hpoleselo/SSFR/latex/imagens/kpeKi.jpg

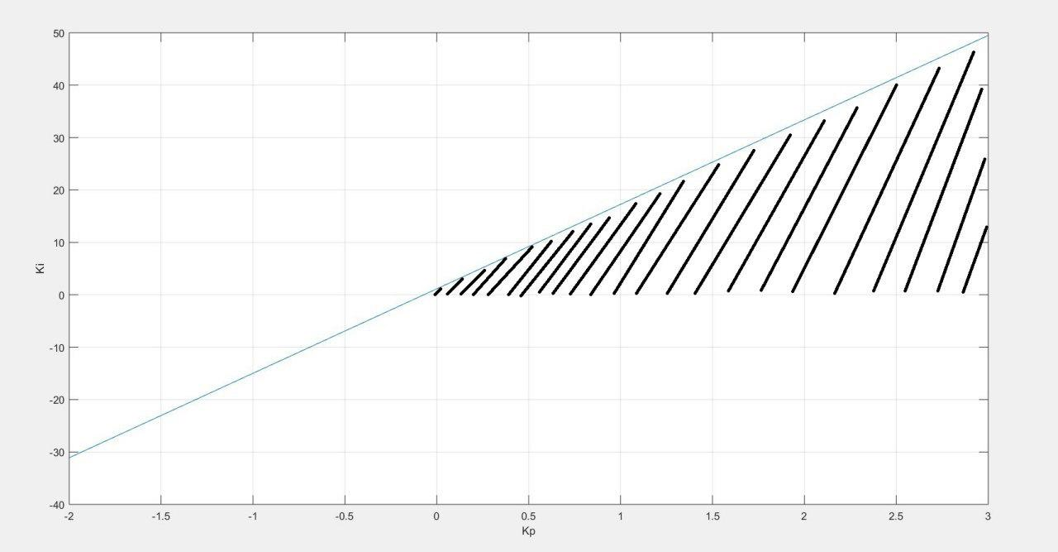
latex/imagens/kpeKi.jpg
