hpoleselo/SSFR/src/calib_images/left-0000.png

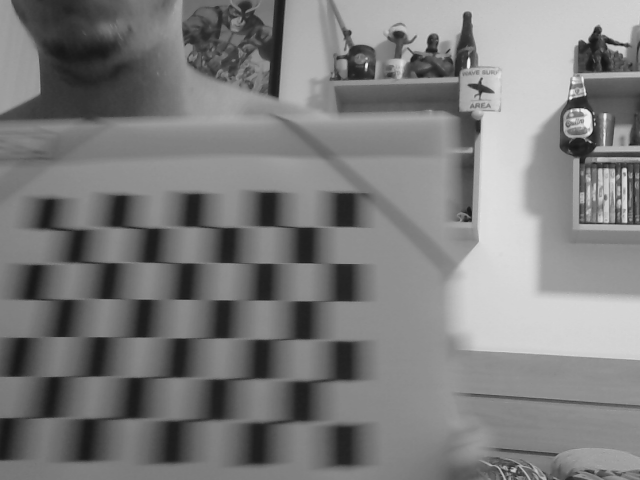
src/calib_images/left-0000.png
