hpoleselo/SSFR/src/calib_images/left-0001.png

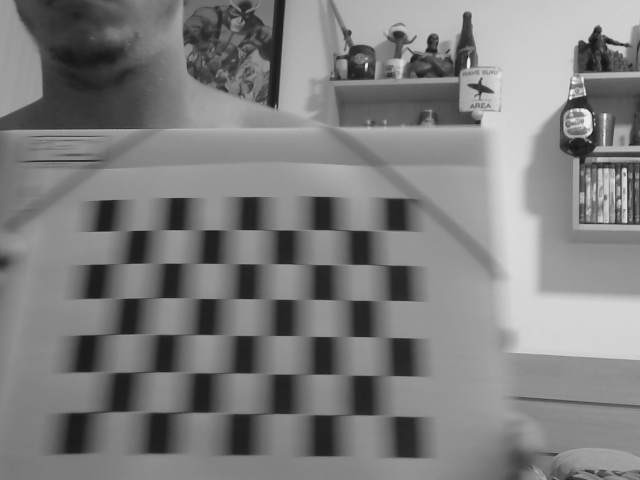
src/calib_images/left-0001.png
