hpoleselo/SSFR/src/calib_images/left-0002.png

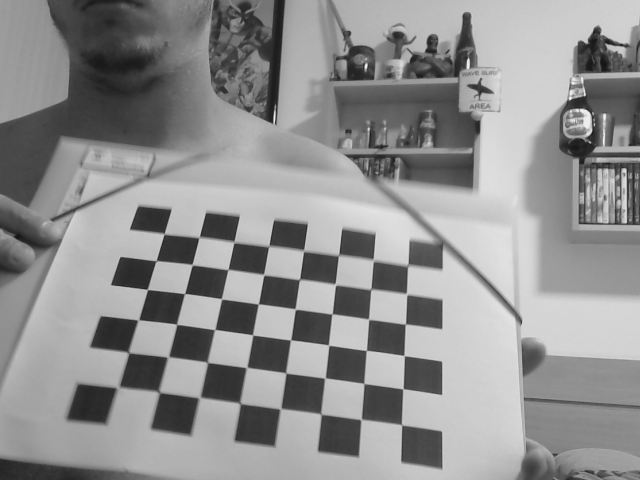
src/calib_images/left-0002.png
