hpoleselo/SSFR/src/calib_images/left-0003.png

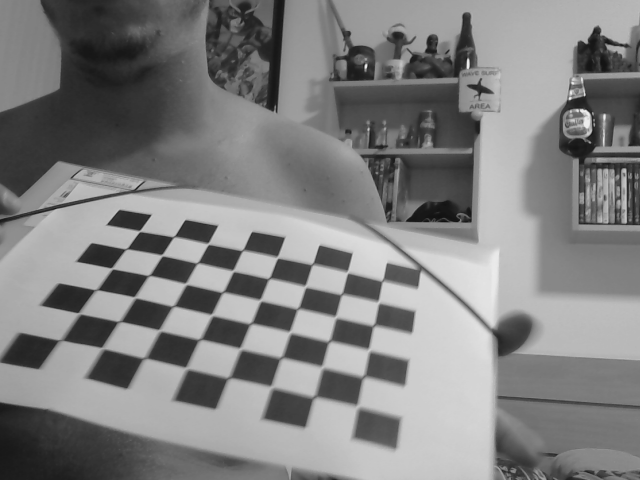
src/calib_images/left-0003.png
