hpoleselo/SSFR/src/calib_images/left-0004.png

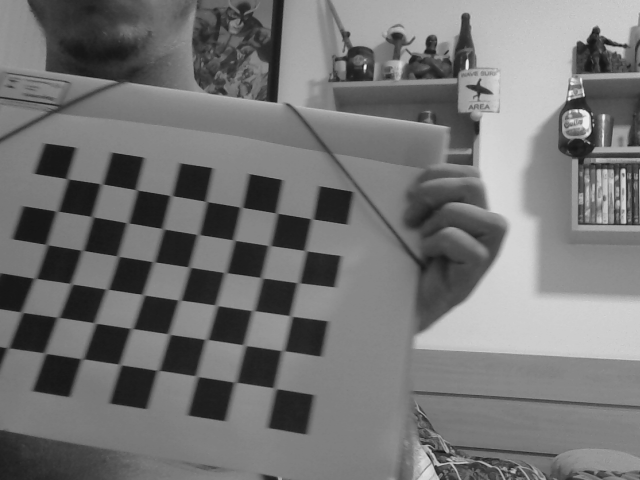
src/calib_images/left-0004.png
