hpoleselo/SSFR/src/calib_images/left-0005.png

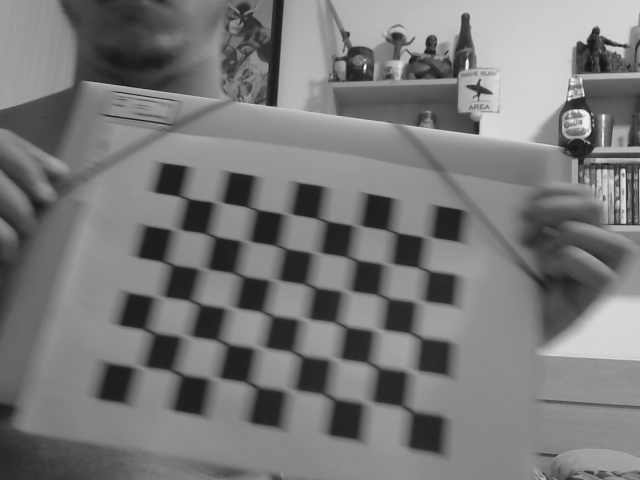
src/calib_images/left-0005.png
