hpoleselo/SSFR/src/calib_images/left-0006.png

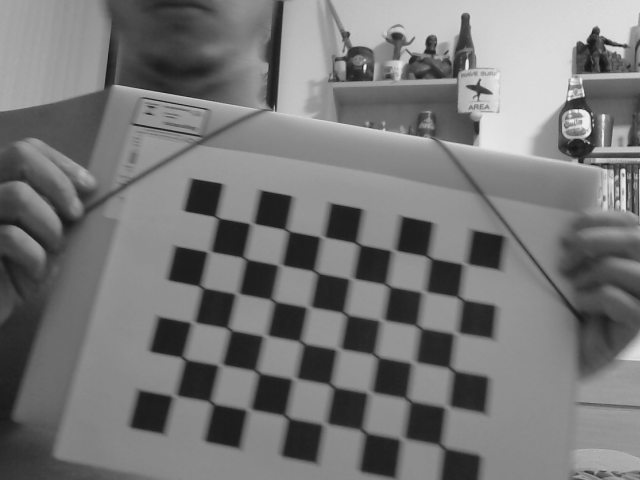
src/calib_images/left-0006.png
