hpoleselo/SSFR/src/calib_images/left-0007.png

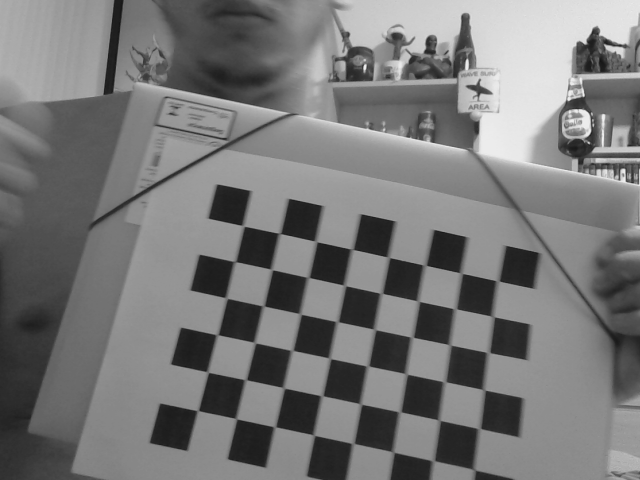
src/calib_images/left-0007.png
