hpoleselo/SSFR/src/calib_images/left-0008.png

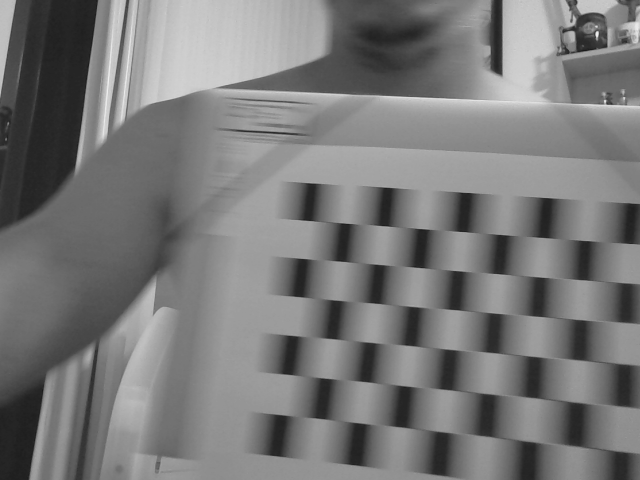
src/calib_images/left-0008.png
