hpoleselo/SSFR/src/calib_images/left-0009.png

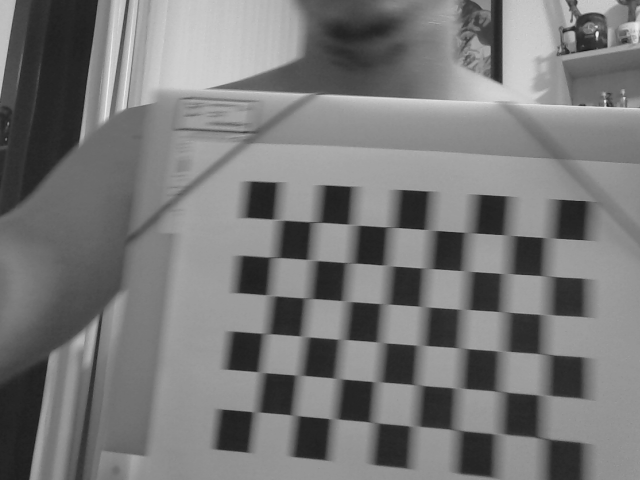
src/calib_images/left-0009.png
