hpoleselo/SSFR/src/calib_images/left-0010.png

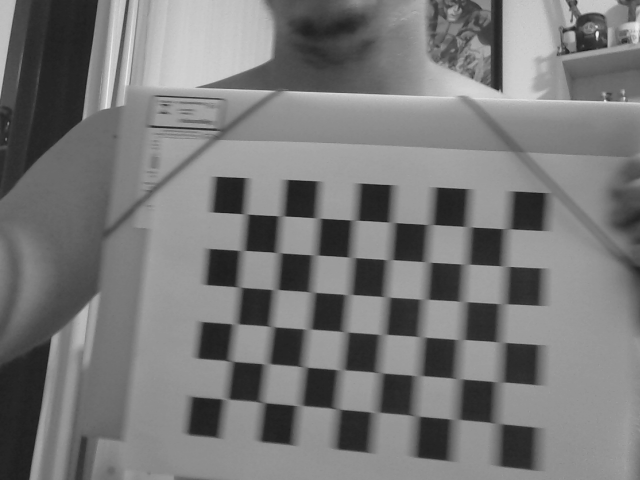
src/calib_images/left-0010.png
