hpoleselo/SSFR/src/calib_images/left-0011.png

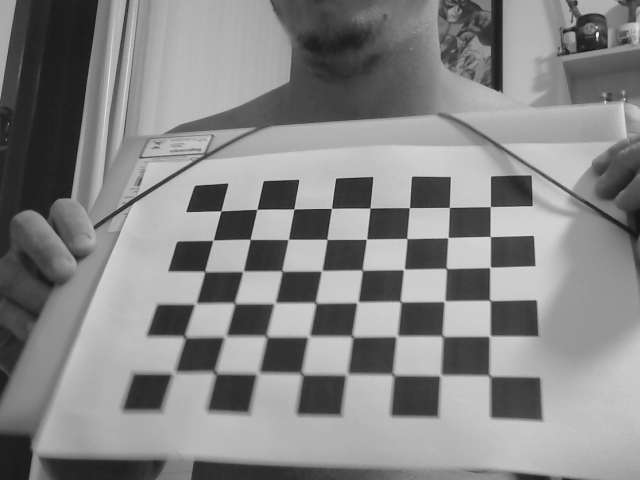
src/calib_images/left-0011.png
