hpoleselo/SSFR/src/calib_images/left-0012.png

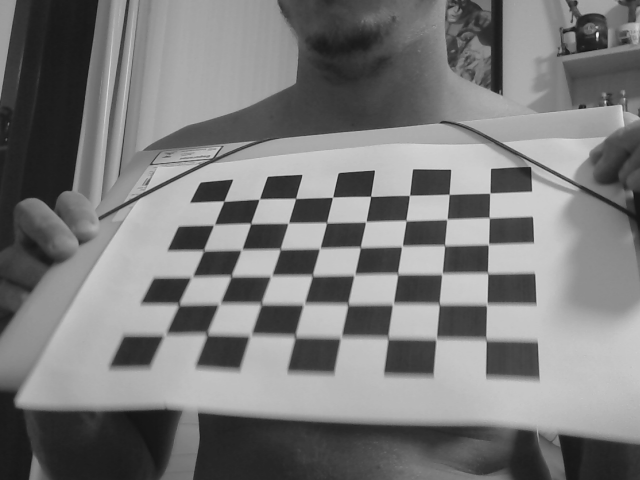
src/calib_images/left-0012.png
