hpoleselo/SSFR/src/calib_images/left-0013.png

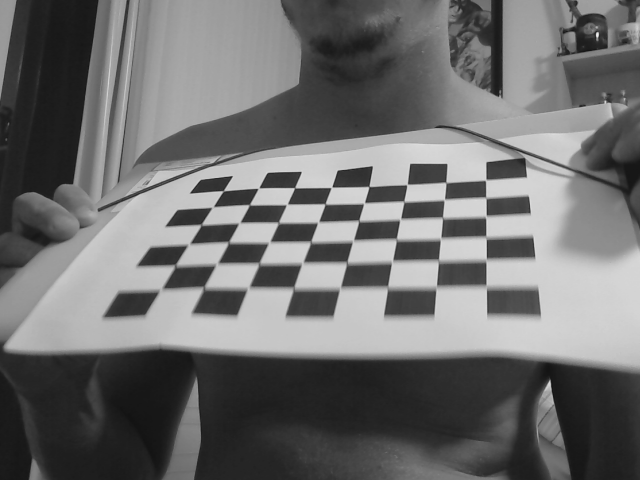
src/calib_images/left-0013.png
