hpoleselo/SSFR/src/calib_images/left-0014.png

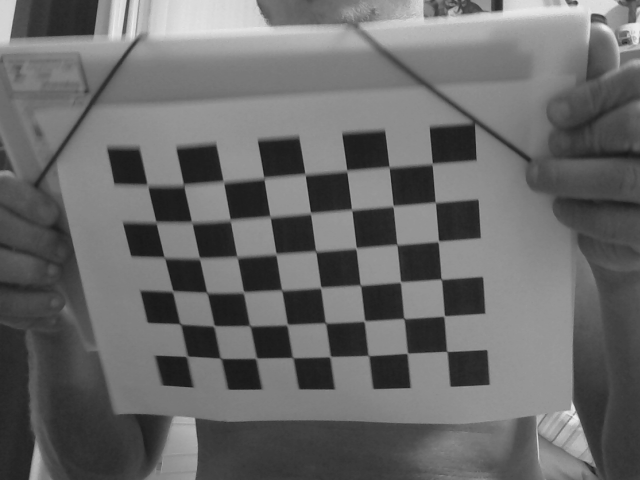
src/calib_images/left-0014.png
