hpoleselo/SSFR/src/calib_images/left-0015.png

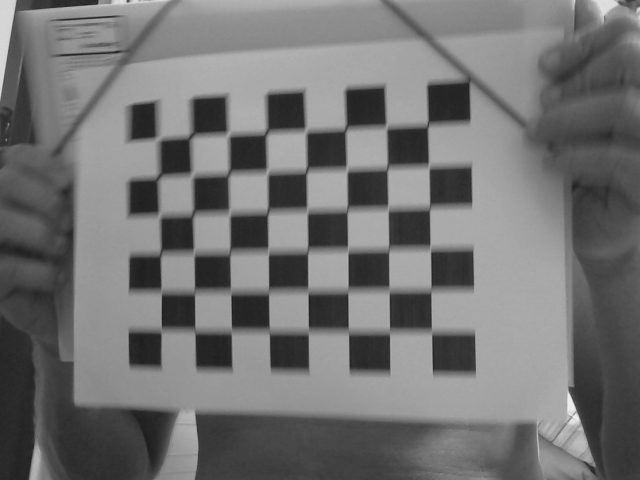
src/calib_images/left-0015.png
