hpoleselo/SSFR/src/calib_images/left-0016.png

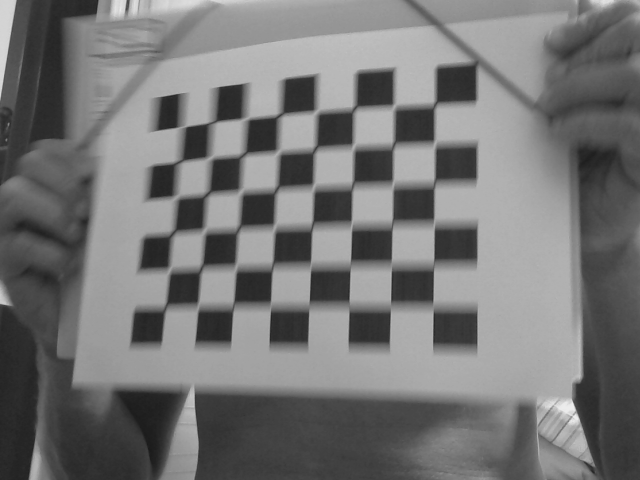
src/calib_images/left-0016.png
