hpoleselo/SSFR/src/calib_images/left-0017.png

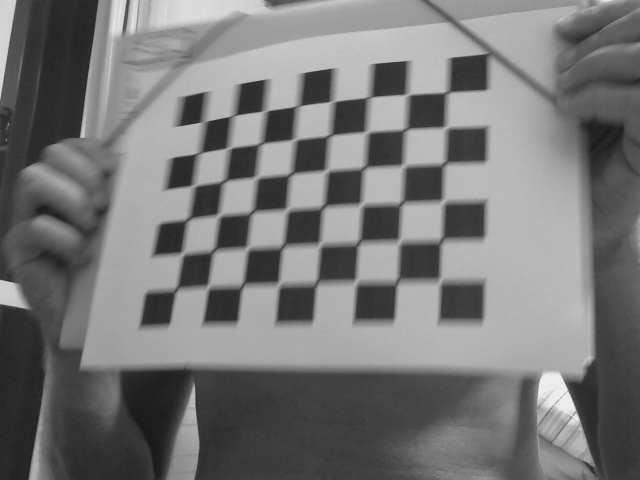
src/calib_images/left-0017.png
