hpoleselo/SSFR/src/calib_images/left-0018.png

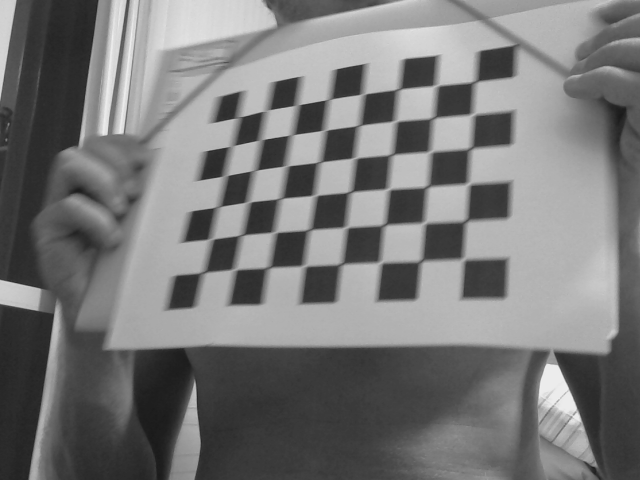
src/calib_images/left-0018.png
