hpoleselo/SSFR/src/calib_images/left-0019.png

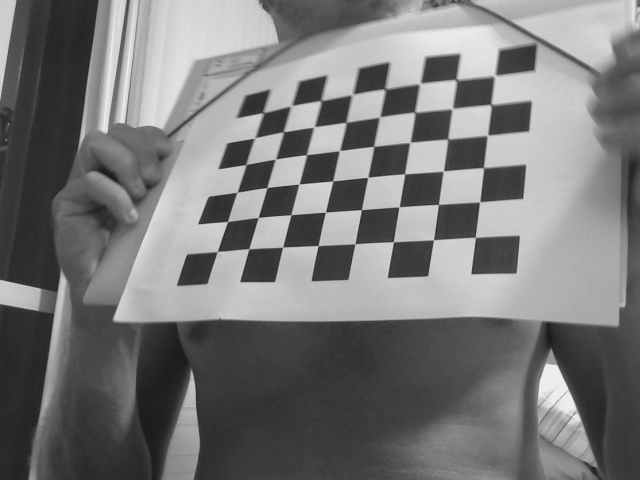
src/calib_images/left-0019.png
