hpoleselo/SSFR/src/calib_images/left-0020.png

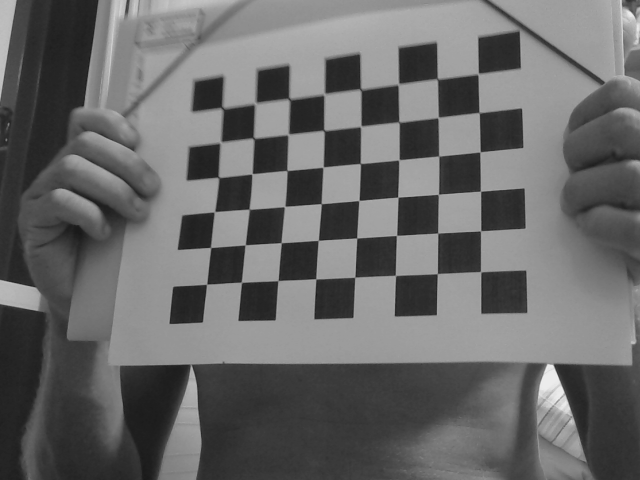
src/calib_images/left-0020.png
