hpoleselo/SSFR/src/calib_images/left-0021.png

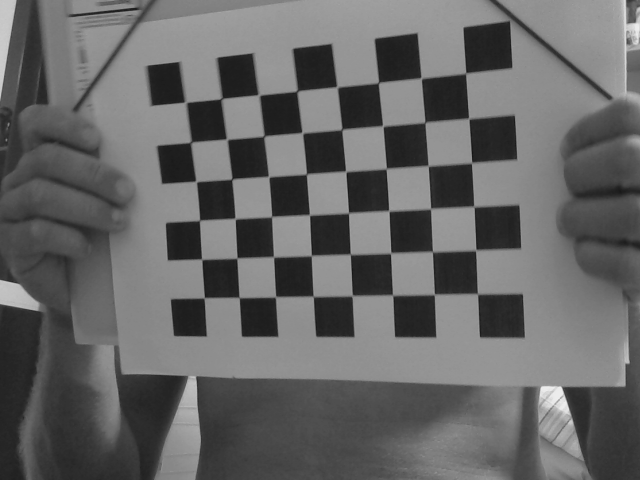
src/calib_images/left-0021.png
