hpoleselo/SSFR/src/calib_images/left-0022.png

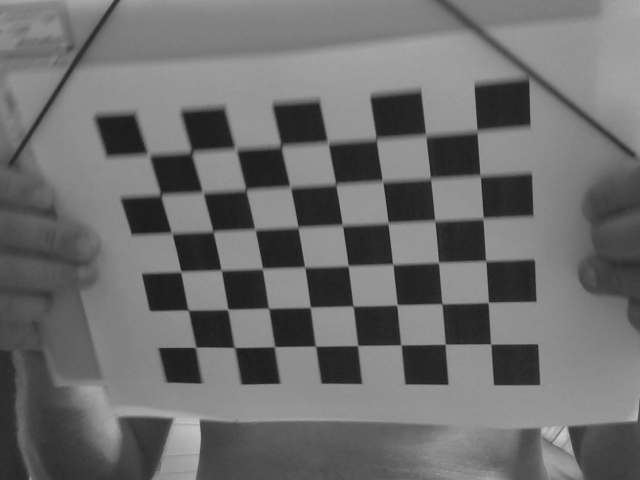
src/calib_images/left-0022.png
