hpoleselo/SSFR/src/calib_images/left-0023.png

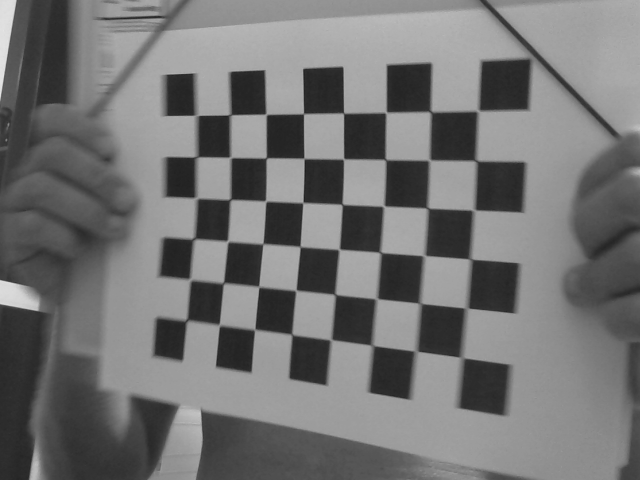
src/calib_images/left-0023.png
