hpoleselo/SSFR/src/calib_images/left-0024.png

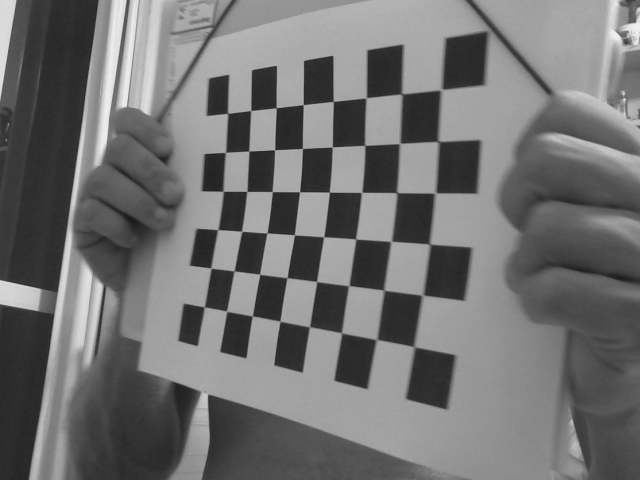
src/calib_images/left-0024.png
