hpoleselo/SSFR/src/calib_images/left-0025.png

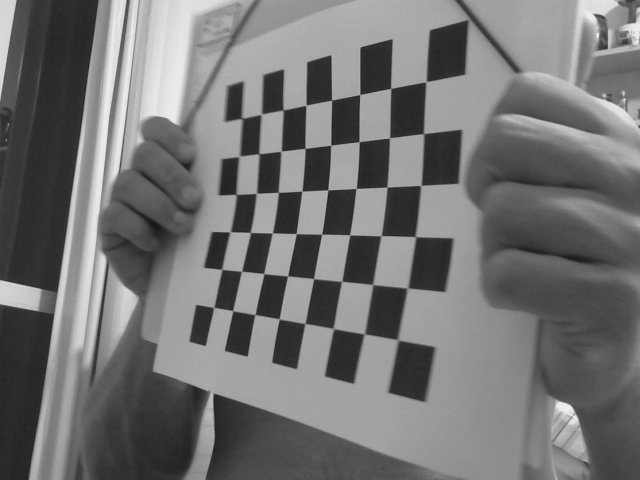
src/calib_images/left-0025.png
