hpoleselo/SSFR/src/calib_images/left-0026.png

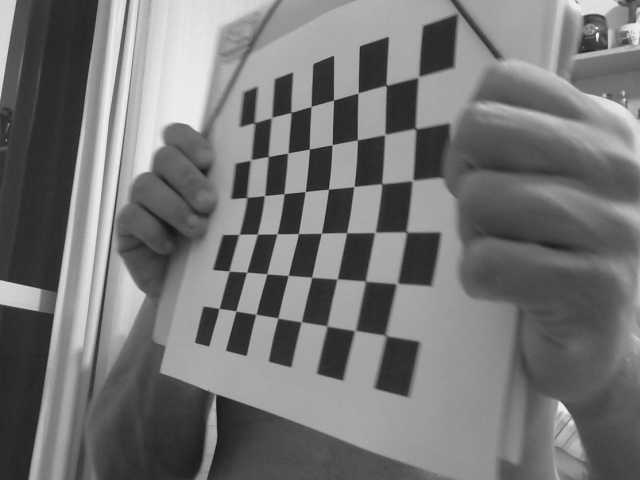
src/calib_images/left-0026.png
