hpoleselo/SSFR/src/calib_images/left-0027.png

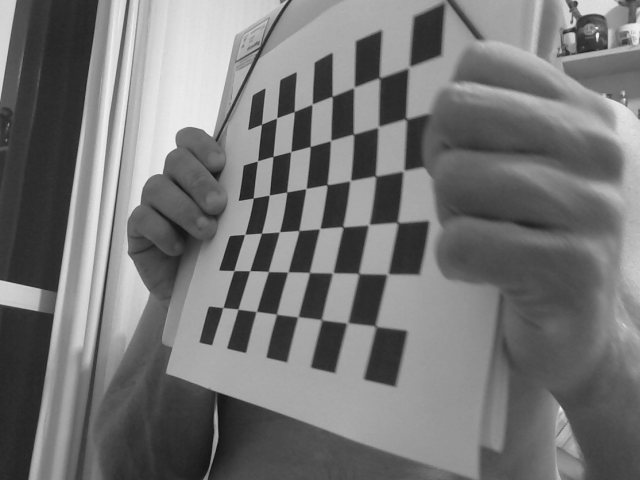
src/calib_images/left-0027.png
