hpoleselo/SSFR/src/calib_images/left-0028.png

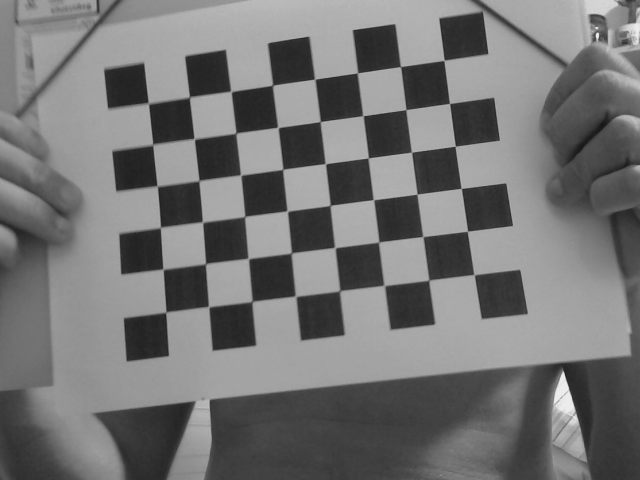
src/calib_images/left-0028.png
