hpoleselo/SSFR/src/calib_images/left-0029.png

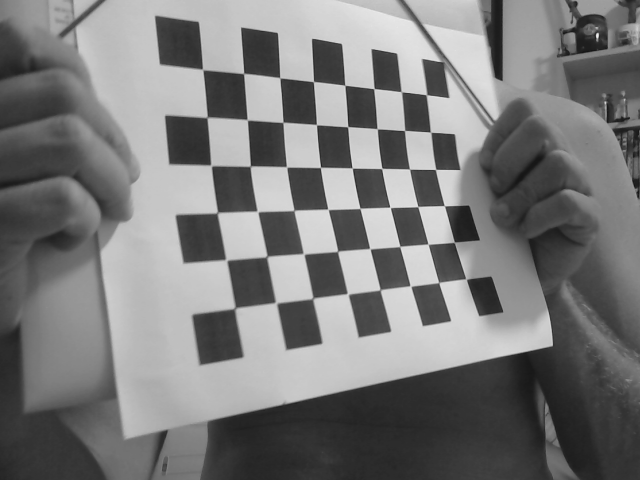
src/calib_images/left-0029.png
