hpoleselo/SSFR/src/calib_images/left-0031.png

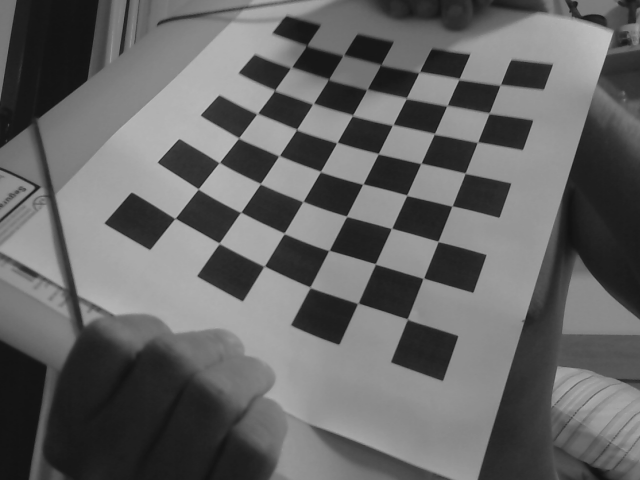
src/calib_images/left-0031.png
