hpoleselo/SSFR/src/calib_images/left-0032.png

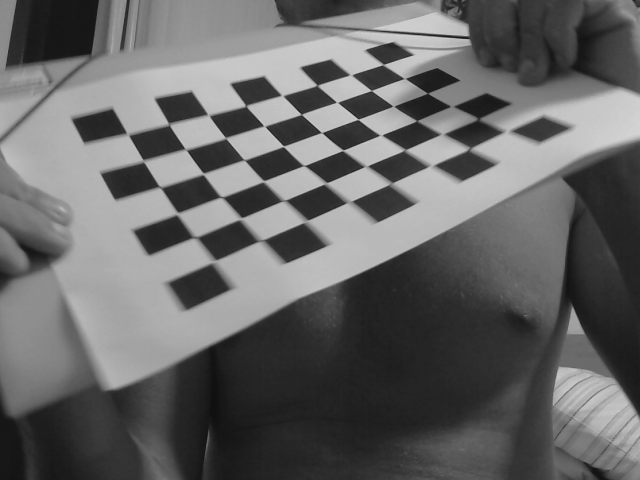
src/calib_images/left-0032.png
