hpoleselo/SSFR/src/calib_images/left-0034.png

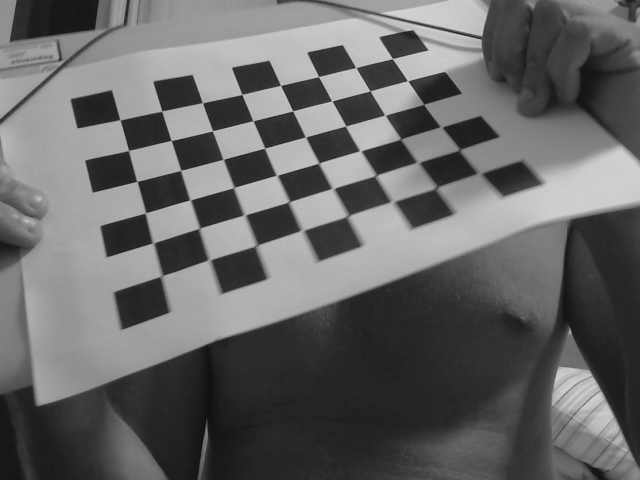
src/calib_images/left-0034.png
