hpoleselo/SSFR/src/calib_images/left-0035.png

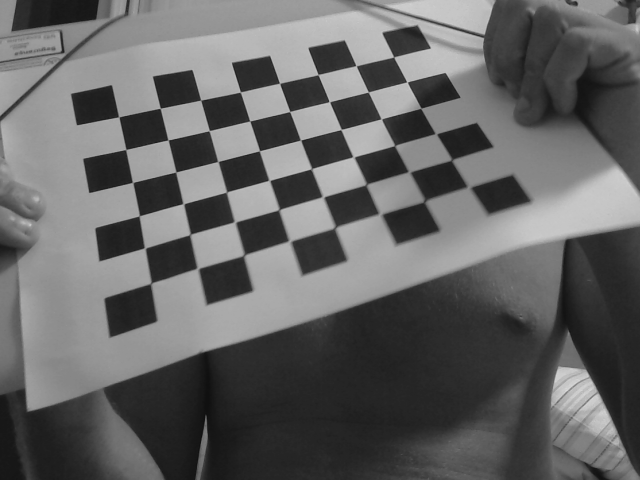
src/calib_images/left-0035.png
