hpoleselo/SSFR/src/calib_images/left-0036.png

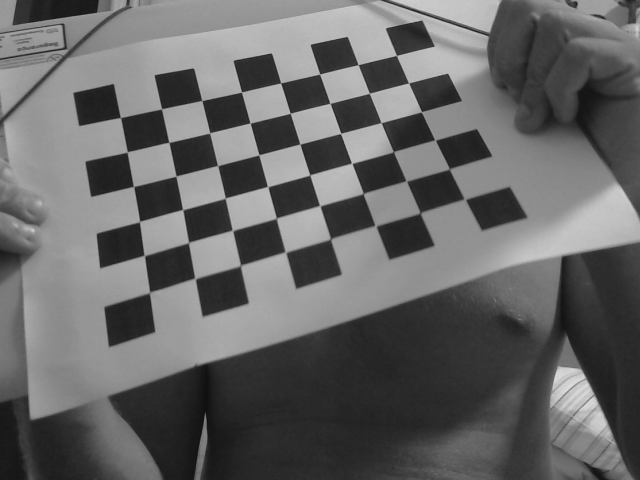
src/calib_images/left-0036.png
