hpoleselo/SSFR/src/calib_images/left-0037.png

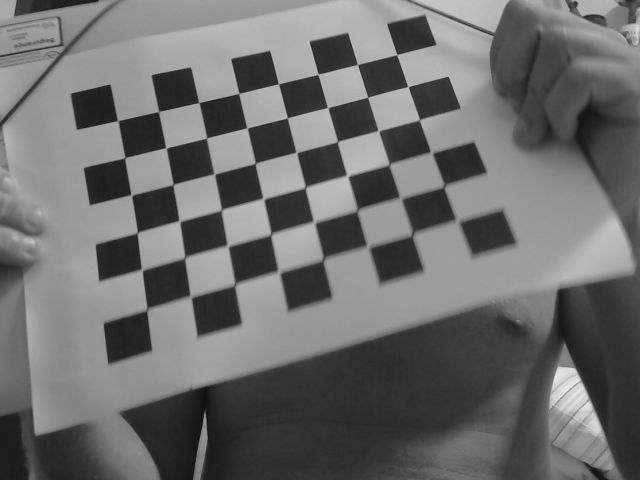
src/calib_images/left-0037.png
