hpoleselo/SSFR/src/calib_images/left-0038.png

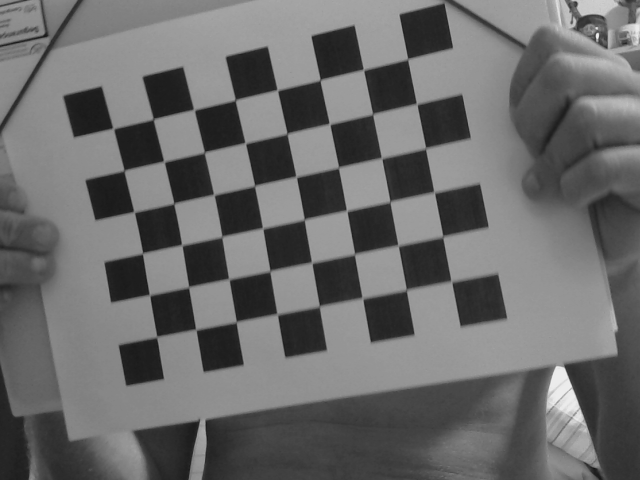
src/calib_images/left-0038.png
