hpoleselo/SSFR/src/calib_images/left-0039.png

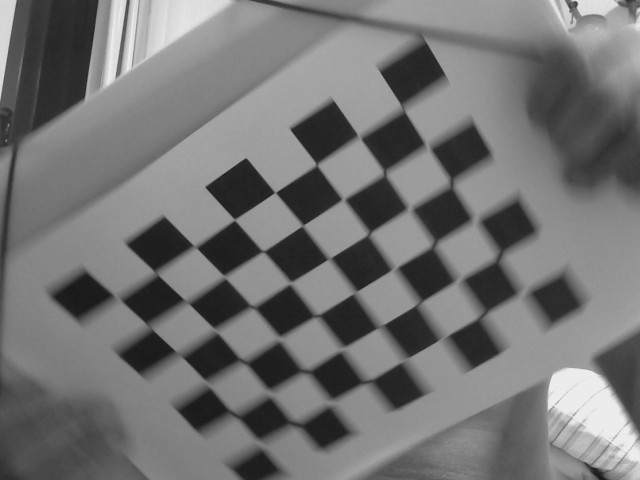
src/calib_images/left-0039.png
