hpoleselo/SSFR/src/calib_images/left-0040.png

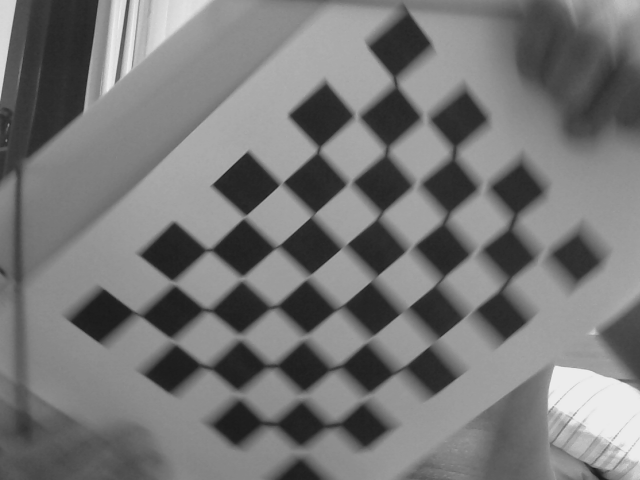
src/calib_images/left-0040.png
