hpoleselo/SSFR/src/calib_images/left-0041.png

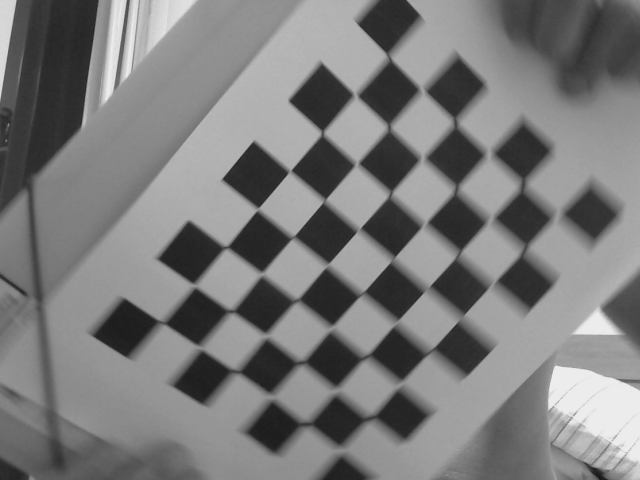
src/calib_images/left-0041.png
