hpoleselo/SSFR/src/calib_images/left-0042.png

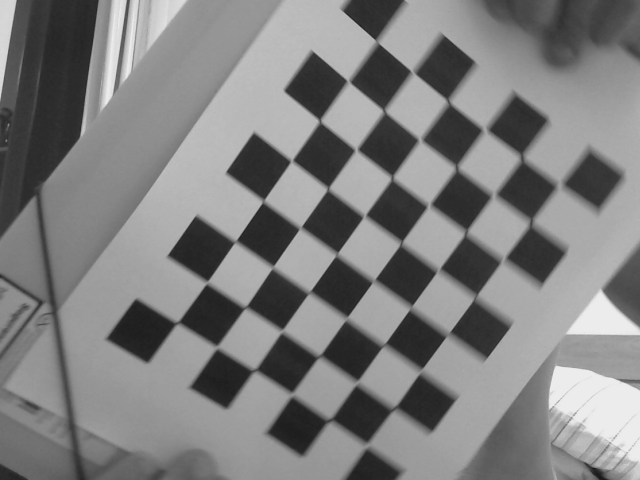
src/calib_images/left-0042.png
