hpoleselo/SSFR/src/calib_images/left-0043.png

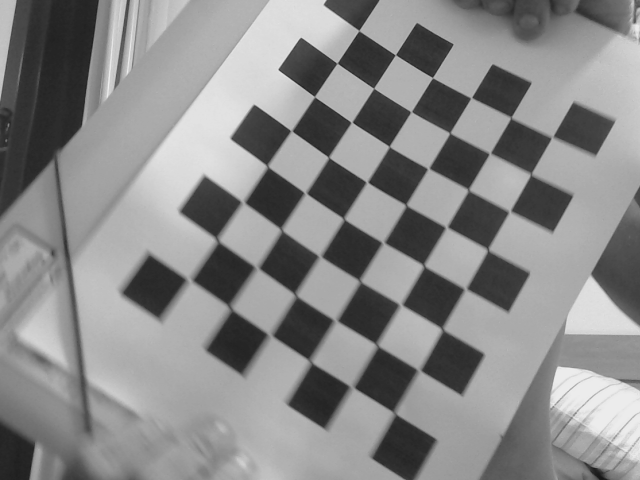
src/calib_images/left-0043.png
