hpoleselo/SSFR/src/calib_images/left-0044.png

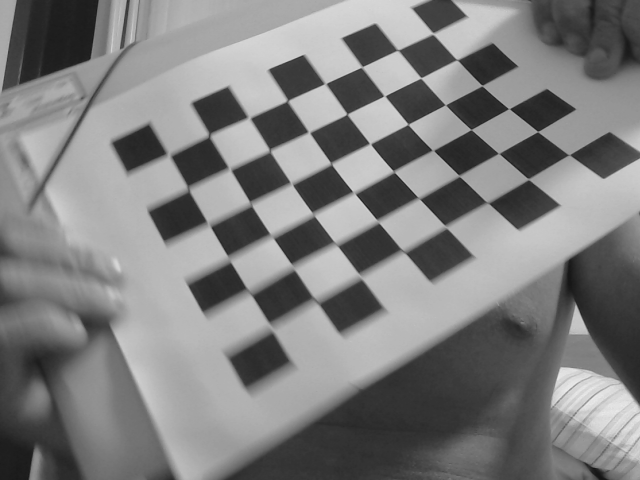
src/calib_images/left-0044.png
