hpoleselo/SSFR/src/calib_images/left-0045.png

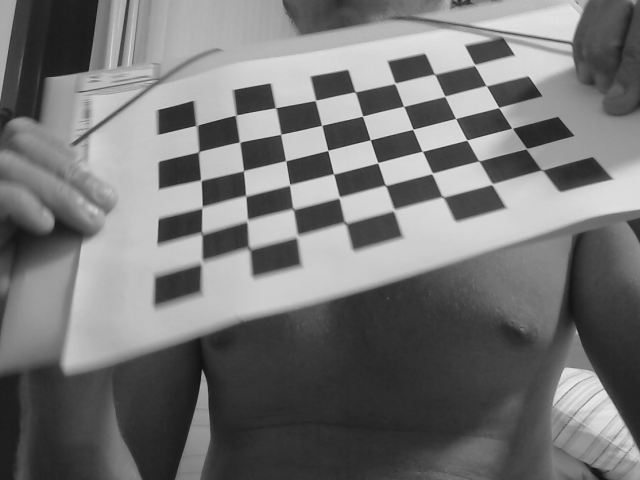
src/calib_images/left-0045.png
