hpoleselo/SSFR/src/calib_images/left-0046.png

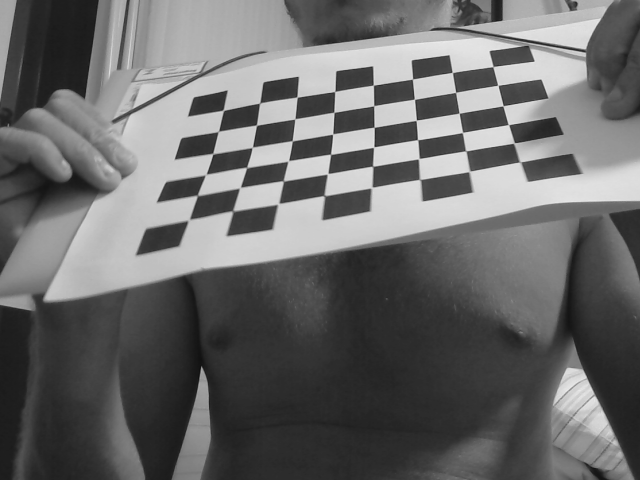
src/calib_images/left-0046.png
