hpoleselo/SSFR/src/calib_images/left-0047.png

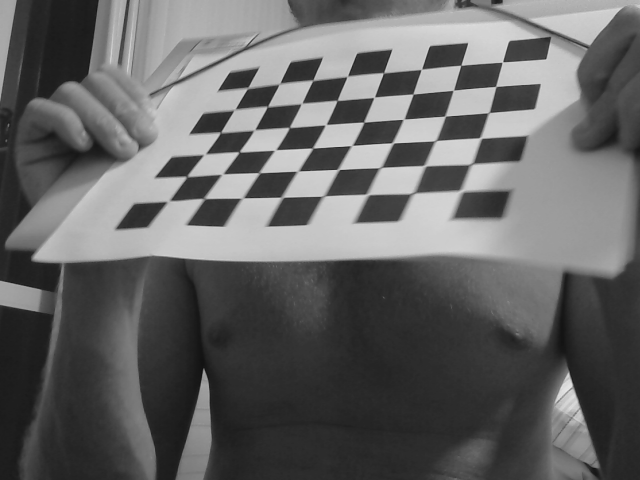
src/calib_images/left-0047.png
