hpoleselo/SSFR/src/calib_images/left-0048.png

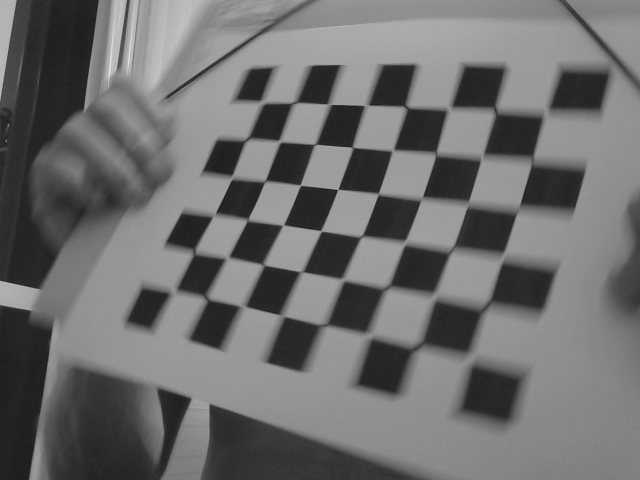
src/calib_images/left-0048.png
