hpoleselo/SSFR/src/calib_images/left-0049.png

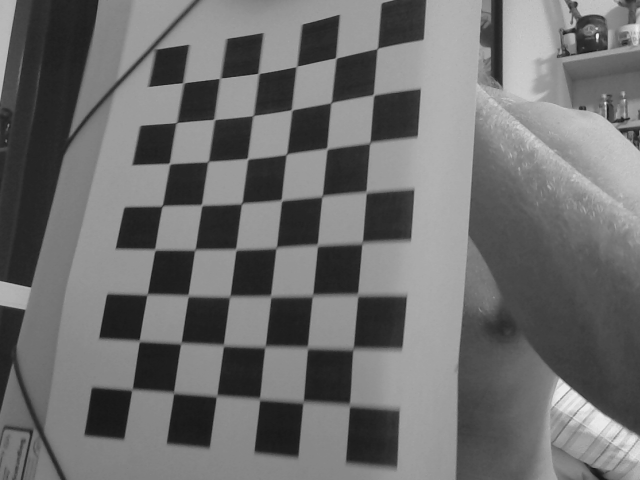
src/calib_images/left-0049.png
