hpoleselo/SSFR/src/calib_images/left-0050.png

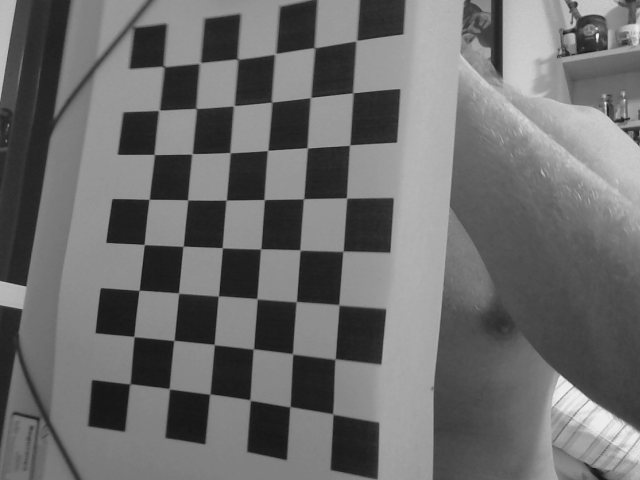
src/calib_images/left-0050.png
