hpoleselo/SSFR/src/calib_images/left-0051.png

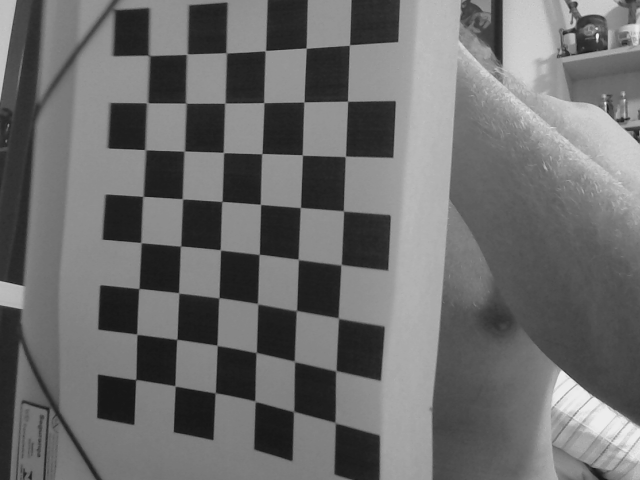
src/calib_images/left-0051.png
