hpoleselo/SSFR/src/calib_images/left-0052.png

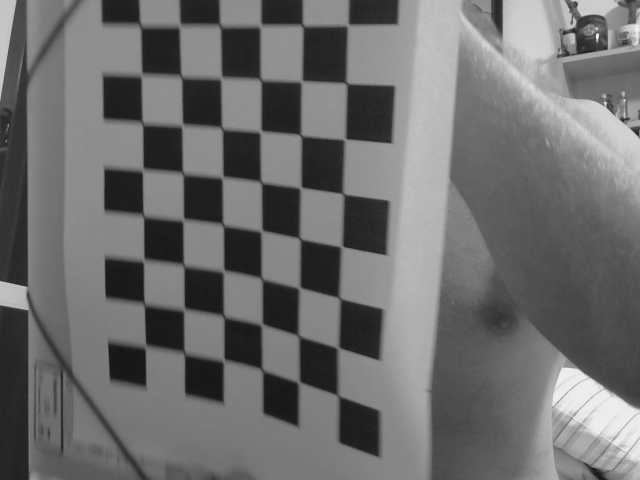
src/calib_images/left-0052.png
