hpoleselo/SSFR/src/calib_images/left-0053.png

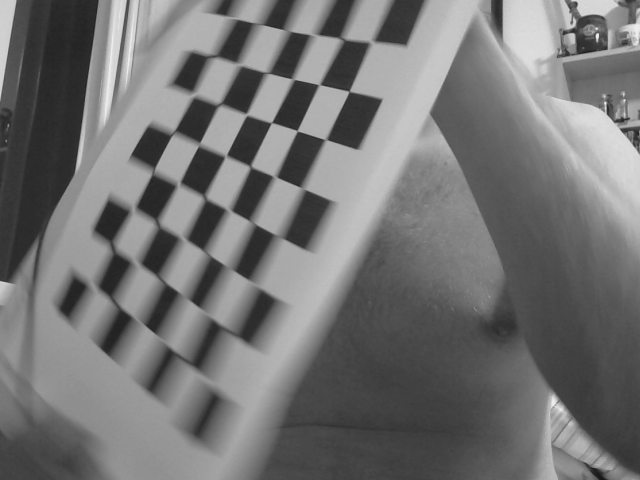
src/calib_images/left-0053.png
