hpoleselo/SSFR/src/calib_images/left-0054.png

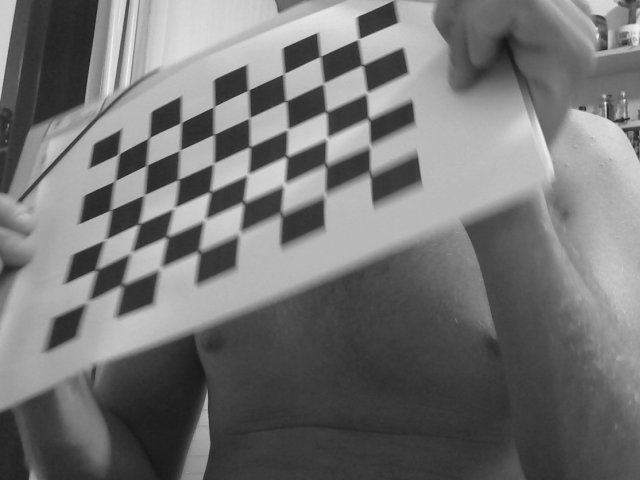
src/calib_images/left-0054.png
