hpoleselo/SSFR/src/calib_images/left-0055.png

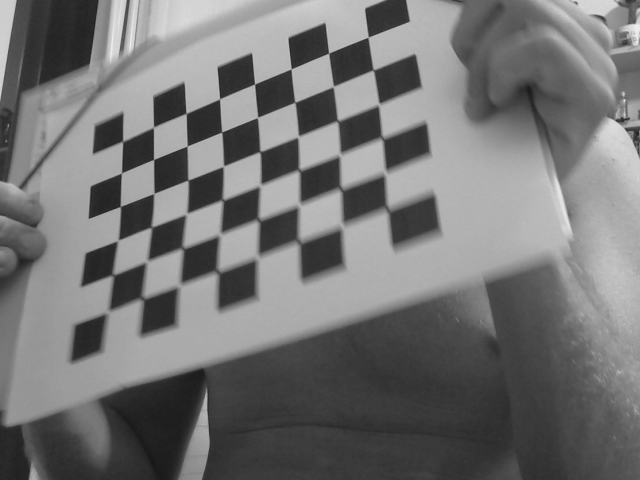
src/calib_images/left-0055.png
