hpoleselo/SSFR/src/calib_images/left-0056.png

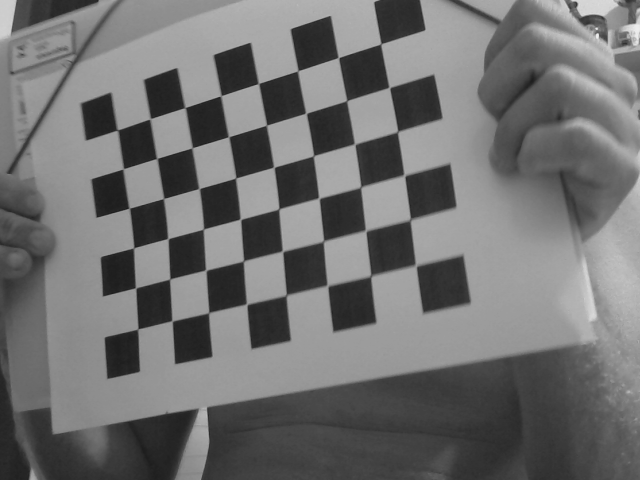
src/calib_images/left-0056.png
