hpoleselo/SSFR/src/calib_images/left-0057.png

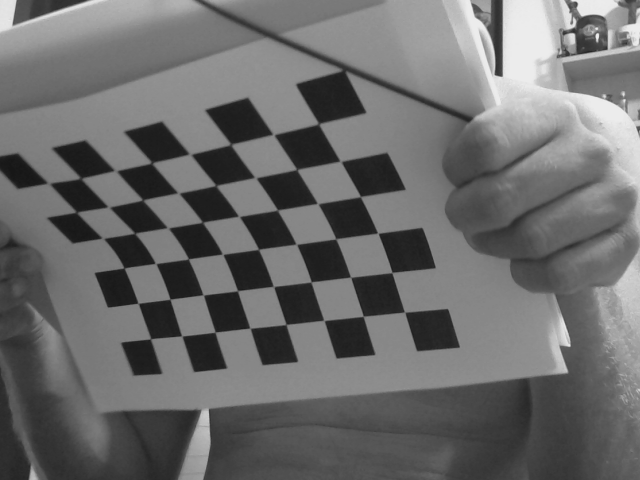
src/calib_images/left-0057.png
