hpoleselo/SSFR/src/calib_images/left-0058.png

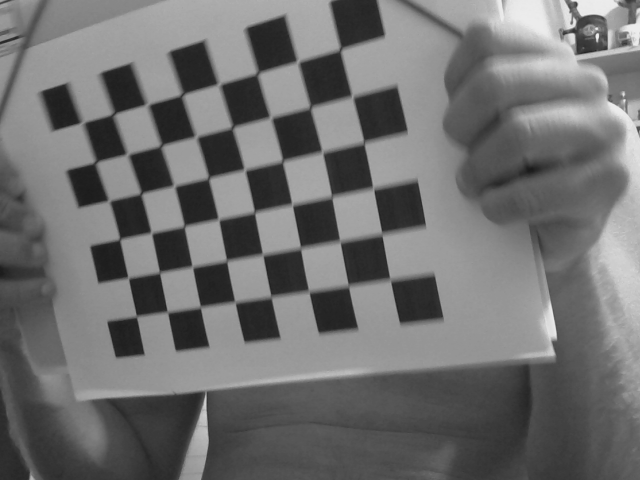
src/calib_images/left-0058.png
