hpoleselo/SSFR/src/calib_images/left-0059.png

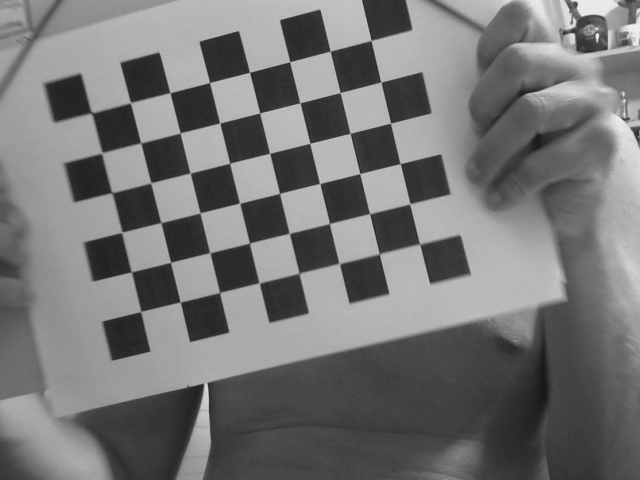
src/calib_images/left-0059.png
