hpoleselo/SSFR/src/calib_images/left-0060.png

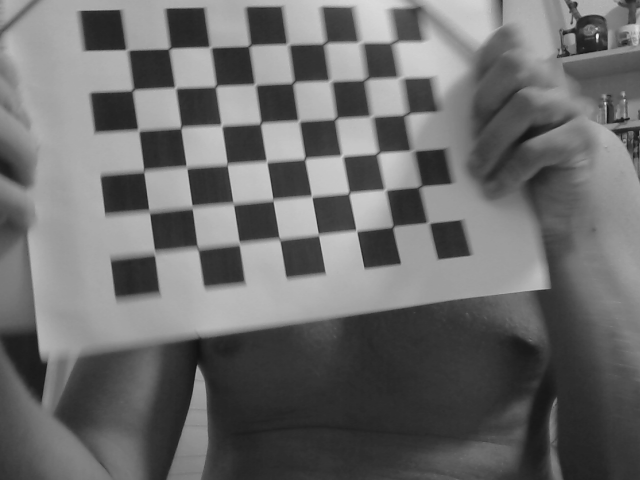
src/calib_images/left-0060.png
