hpoleselo/SSFR/src/calib_images/left-0061.png

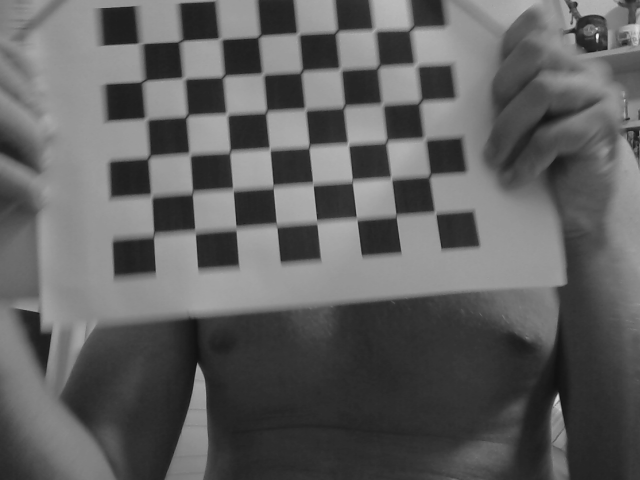
src/calib_images/left-0061.png
