hpoleselo/SSFR/src/calib_images/left-0062.png

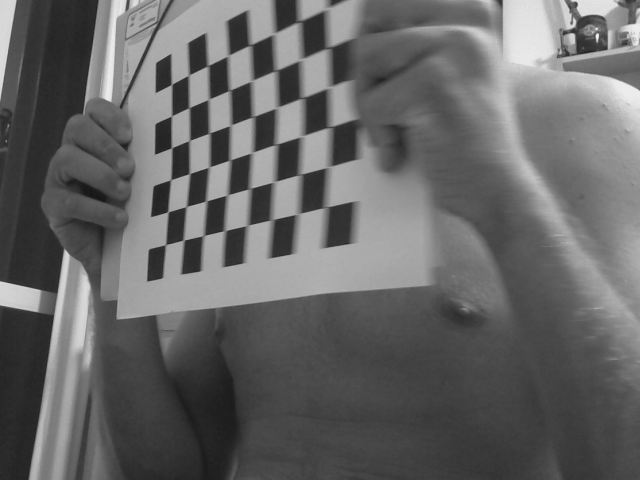
src/calib_images/left-0062.png
