hpoleselo/SSFR/src/calib_images/left-0063.png

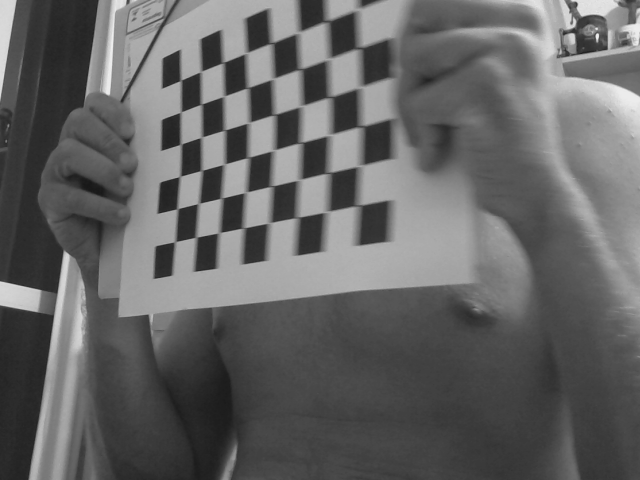
src/calib_images/left-0063.png
