hpoleselo/SSFR/src/calib_images/left-0064.png

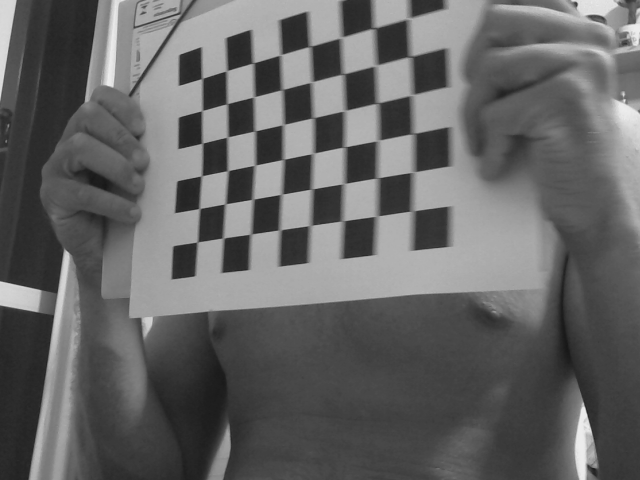
src/calib_images/left-0064.png
