hpoleselo/SSFR/src/calib_images/left-0065.png

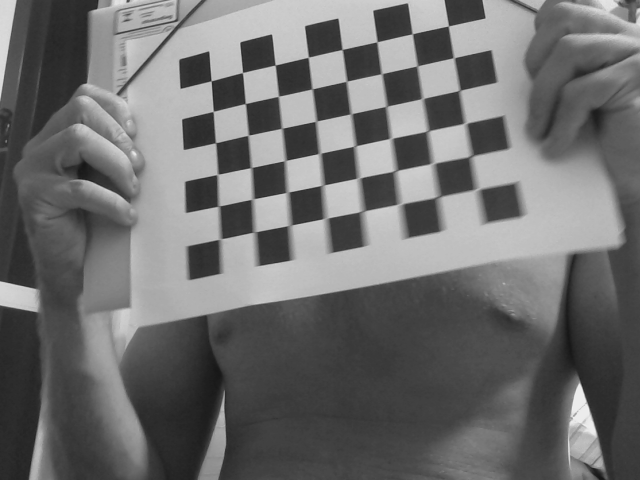
src/calib_images/left-0065.png
