hpoleselo/SSFR/src/calib_images/left-0066.png

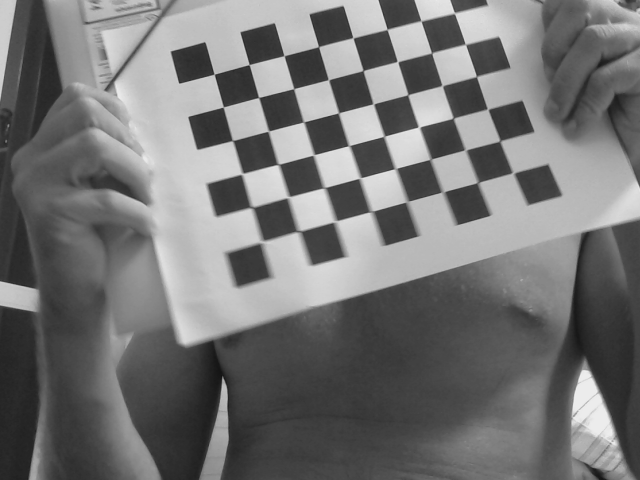
src/calib_images/left-0066.png
