hpoleselo/SSFR/src/calib_images/left-0067.png

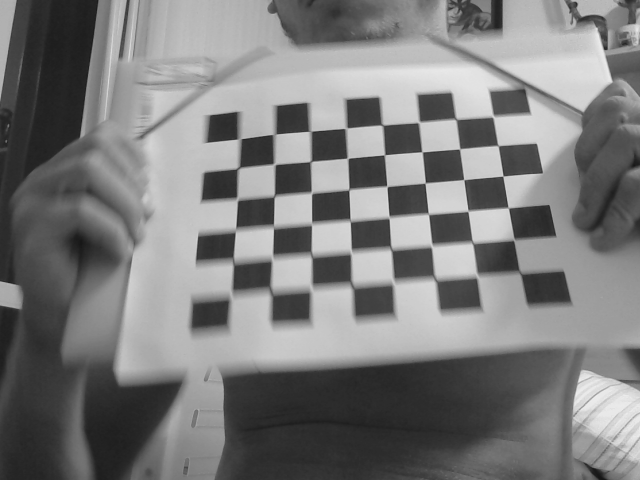
src/calib_images/left-0067.png
