hpoleselo/SSFR/src/calib_images/left-0068.png

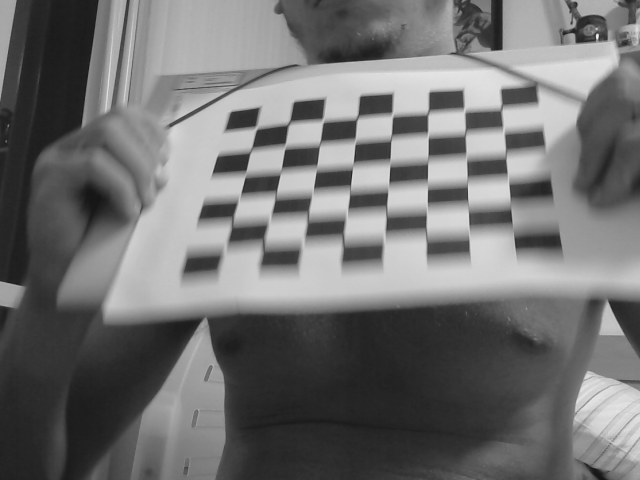
src/calib_images/left-0068.png
