hpoleselo/SSFR/src/calib_images/left-0069.png

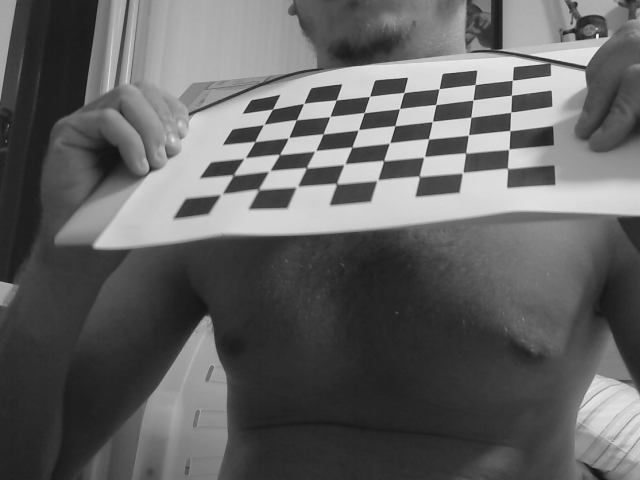
src/calib_images/left-0069.png
