hpoleselo/SSFR/src/calib_images/left-0070.png

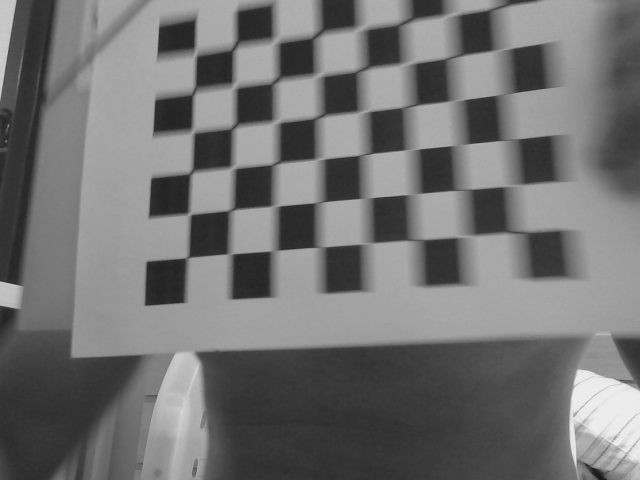
src/calib_images/left-0070.png
