hpoleselo/SSFR/src/calib_images/left-0071.png

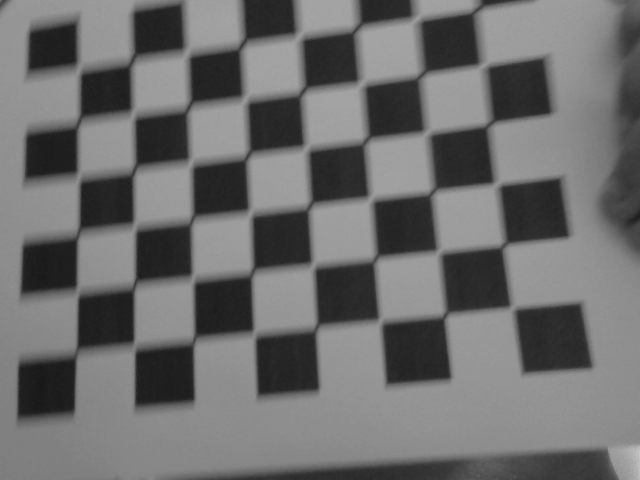
src/calib_images/left-0071.png
