hpoleselo/SSFR/src/calib_images/left-0072.png

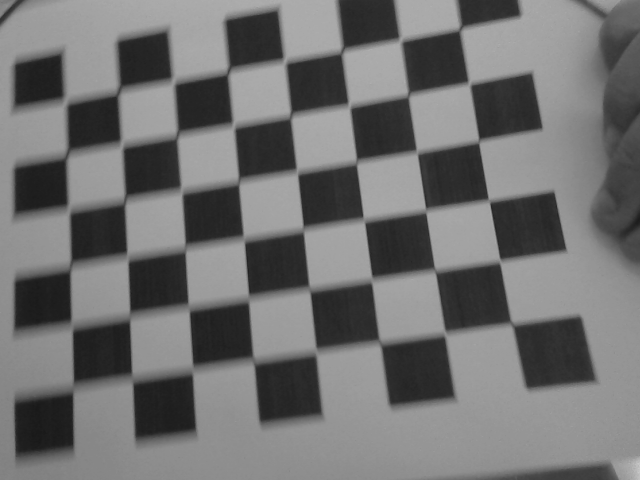
src/calib_images/left-0072.png
