hpoleselo/SSFR/src/calib_images/left-0073.png

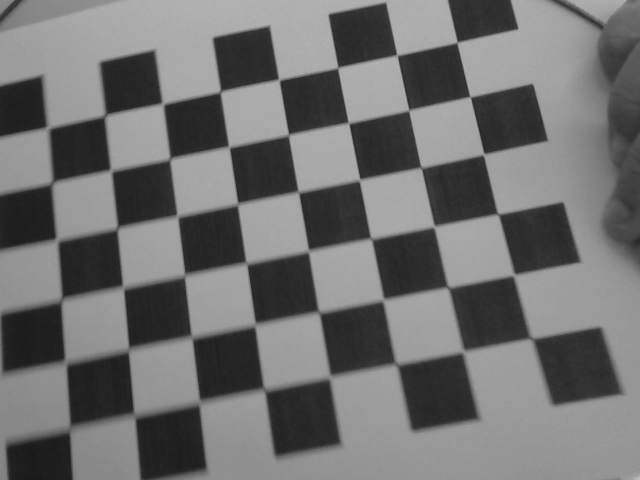
src/calib_images/left-0073.png
