hpoleselo/SSFR/src/calib_images/left-0074.png

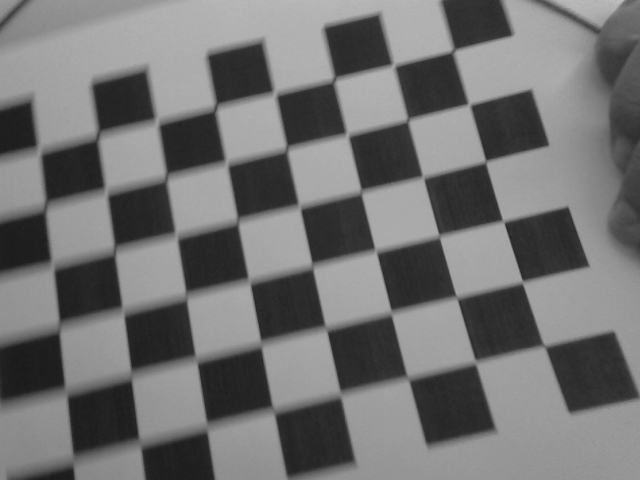
src/calib_images/left-0074.png
