hpoleselo/SSFR/src/calib_images/left-0075.png

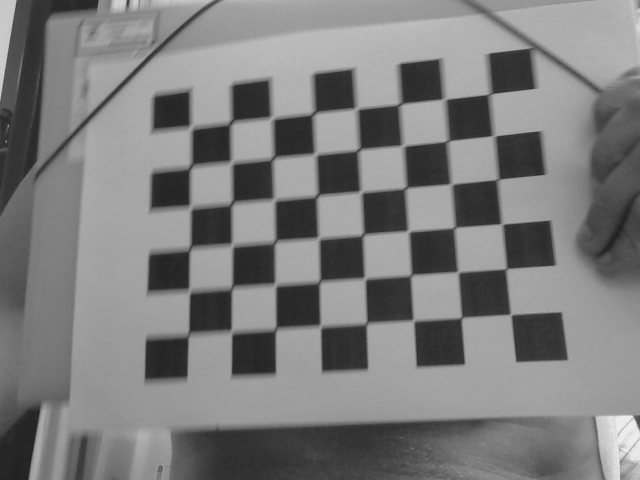
src/calib_images/left-0075.png
