hpoleselo/SSFR/src/calib_images/left-0076.png

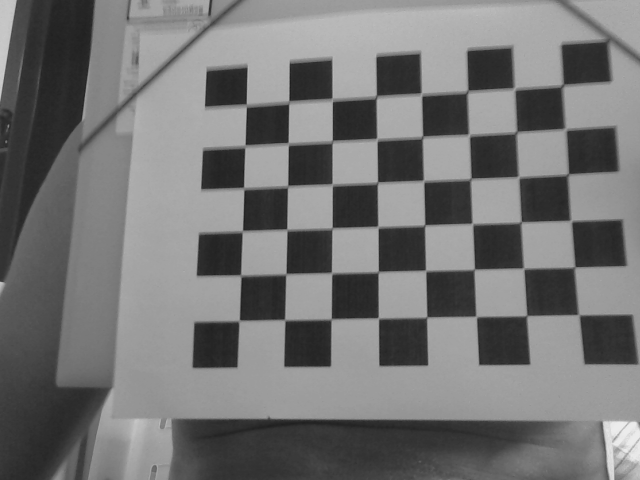
src/calib_images/left-0076.png
