hpoleselo/SSFR/src/calib_images/left-0077.png

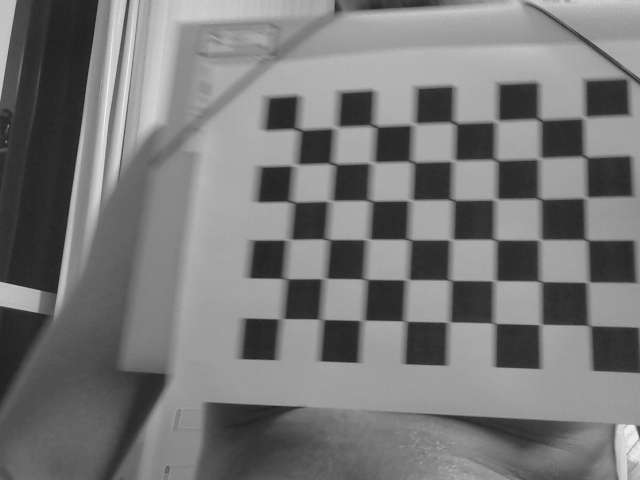
src/calib_images/left-0077.png
