hpoleselo/SSFR/src/calib_images/left-0078.png

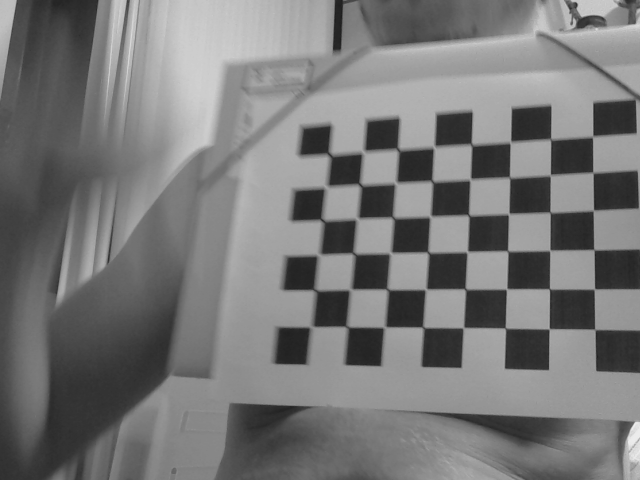
src/calib_images/left-0078.png
