hpoleselo/SSFR/src/calib_images/left-0079.png

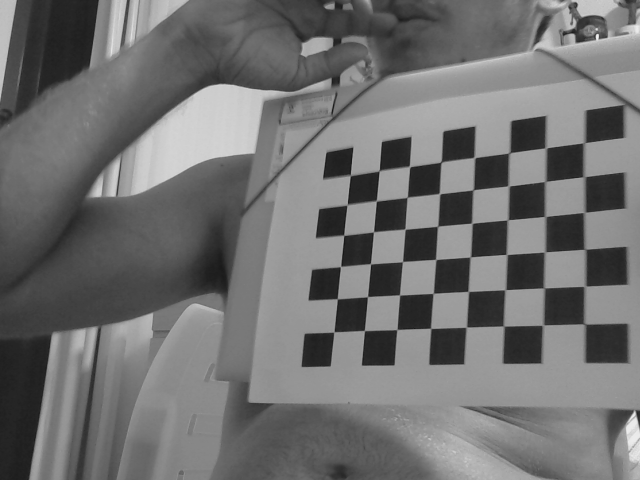
src/calib_images/left-0079.png
