hpoleselo/SSFR/src/calib_images/left-0080.png

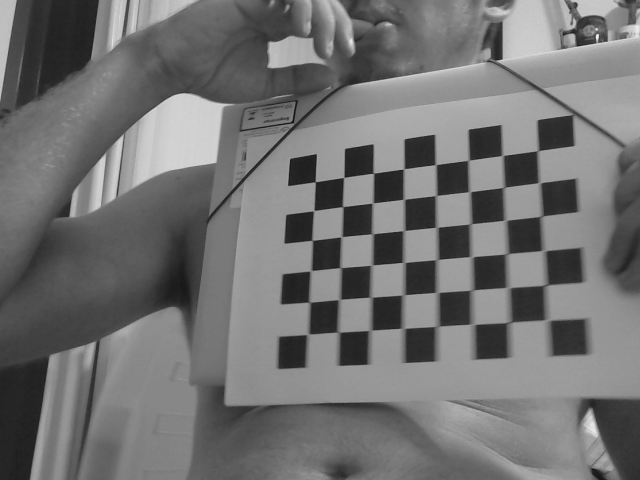
src/calib_images/left-0080.png
