hpoleselo/SSFR/src/calib_images/left-0081.png

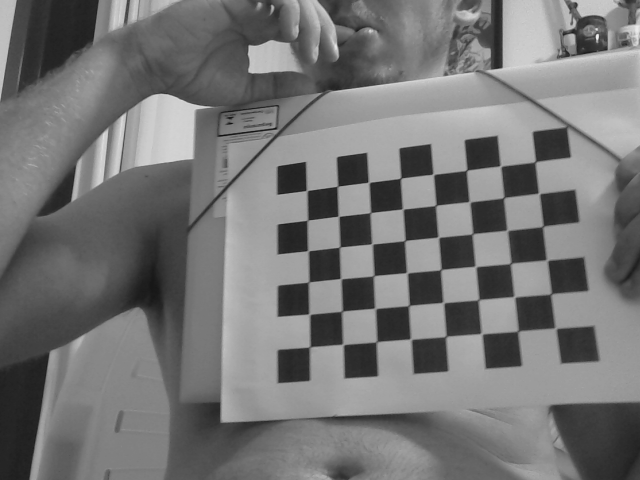
src/calib_images/left-0081.png
