hpoleselo/SSFR/src/calib_images/left-0082.png

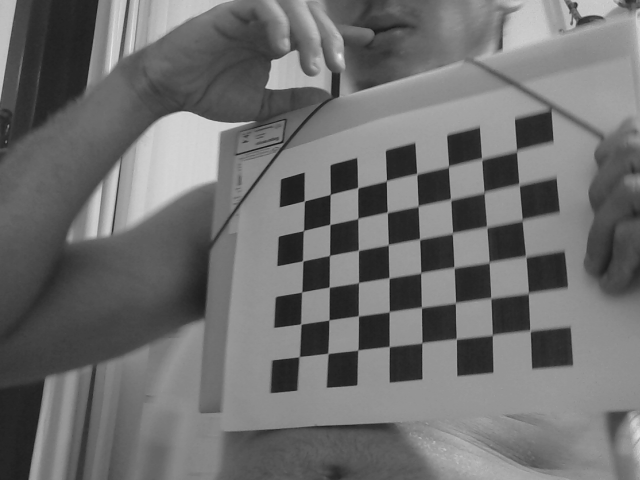
src/calib_images/left-0082.png
