hpoleselo/SSFR/src/calib_images/left-0083.png

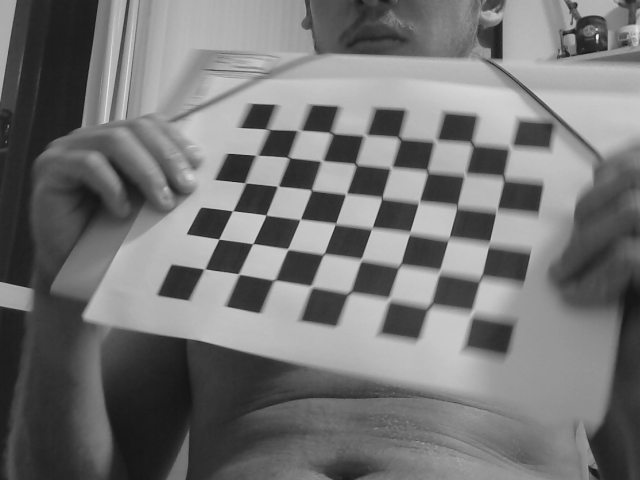
src/calib_images/left-0083.png
