hpoleselo/SSFR/src/calib_images/left-0084.png

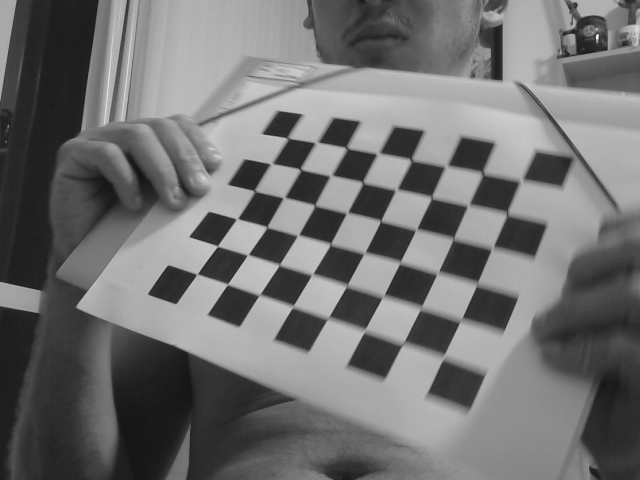
src/calib_images/left-0084.png
