hpoleselo/SSFR/src/calib_images/left-0085.png

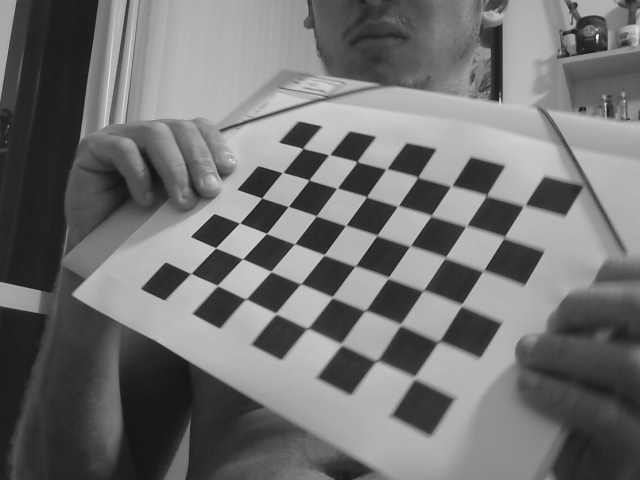
src/calib_images/left-0085.png
