hpoleselo/SSFR/src/calib_images/left-0087.png

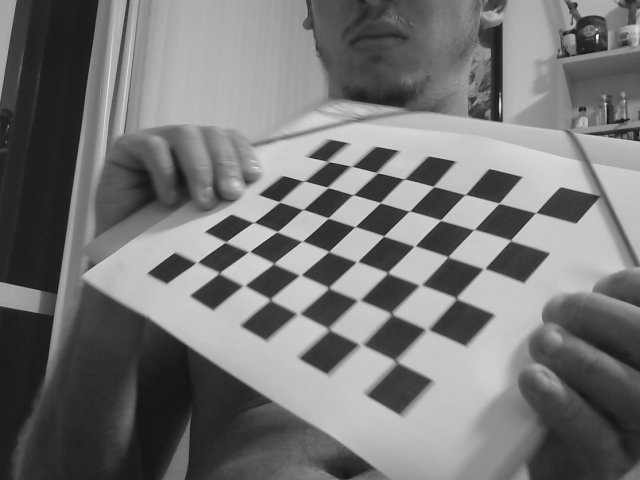
src/calib_images/left-0087.png
